calcumaker/calcumaker/firmware/calcumaker-emu/README.md

# calcumaker-emu

The **Calcumaker 16 emulator** — the real calculator on a host terminal.

This is not a look-alike: it hosts the same `calcumaker_core::App` the firmware
runs. Host keys map to the physical **50-key matrix**, presses resolve through
the **f/g shift layers**, and the display is drawn from the **same TM1640
segment bytes** the hardware receives, rendered as LED-style 7-segment art
(Unicode block elements; `--ascii` falls back to plain `_`/`|` for dumb
terminals). If it works here, the only difference on the device is GPIO.

```
┌──────────────────────────────────────────────────────────────────────────────────────────────────┐
│                         ▄▄▄▄        ▄▄▄▄  ▄▄▄▄  ▄▄▄▄  ▄▄▄▄  ▄▄▄▄  ▄▄▄▄  ▄▄▄▄  ▄▄▄▄  ▄▄▄▄  ▄▄▄▄   │
│    █  █▄▄█     █  █▄▄█   ▄▄█     █   ▄▄█  █▄▄   █▄▄    ▄▄█   ▄▄█     █   ▄▄█  █  █  █▄▄█  █▄▄    │
│    █▗    █     █     █  █▄▄▄     █  ▄▄▄█  ▄▄▄█  █▄▄█  █▄▄▄  ▄▄▄█     █  ▄▄▄█  █▄▄█  ▄▄▄█  ▄▄▄█   │
└──────────────────────────────────────────────────────────────────────────────────────────────────┘
 DEC  prec 256  word unbounded
 X: 1.4142135623730950488016887242096980785696718753769480731766797379907324784621
```

The glass **rounds to its 16 digits** like a real HP (`382.1` shows as `382.1`,
never `382.09999…` spilling off the row); the `X:` line underneath is the SHOW
view — the register at full precision.

## Run it

```sh
brew install gmp mpfr    # one-time host deps (apt: libgmp-dev libmpfr-dev)
cargo run                # interactive; ? shows the key map, Ctrl-C quits
```

Keys mirror the device layout (f = gold shift, g = blue shift):

| Host | Calculator |
| --- | --- |
| `0-9` `a-f` `.` | digits (hex digits radix-permitting), decimal point |
| `+ - * /` | arithmetic |
| `Enter` `Bksp` `X` `n` `E` | ENTER, backspace, CLx, CHS, EEX |
| `S C T L Q P I` | sin cos tan ln √x yˣ 1/x |
| `& \| ^ ~ < >` | AND OR XOR NOT SL SR (X by one bit) |
| `H D O B` | HEX DEC OCT BIN |
| `W` `x` `v` | wsize (X bits, 0=∞), swap, roll-down |
| `m` `r` + `0-f` | STO / RCL, then a digit picks the register |
| `F` `G` | f / g shift — `F`,`E` = π; `F`,`I` = prec; `F`,`W` = sign mode (2's/1's/unsgn); `F`,`&`/`\|`/`^` = RL/RR/ASR; `F`,`a-f` = bit set/clr/test, masks, popcount; `G`,`H/D/O/B` = FIX/SCI/ENG/auto |

In word mode the annunciator line shows the sign mode and the **C** (carry) /
**G** (overflow) flags, 16C style.

## Scripted mode (tests, demos, CI)

`--press` feeds a key string and prints the final frame — `;` (or `\n`) is
ENTER:

```sh
cargo run -- --press "2;3+"          # 2 ENTER 3 +      -> 5
cargo run -- --press "2.0Q"          # sqrt(2.0) to 77 digits at prec 256
cargo run -- --press "17Q"           # integer sqrt: 4, C annunciator (inexact)
cargo run -- --press "2;100P"        # exact 2^100 (integers stay integers)
cargo run -- --press "8W;H0f~"       # 8 wsize, hex, NOT 0F -> F0
cargo run -- --press "16W;15nH"      # -15 @16b 2's comp -> FFF1
cargo run -- --press "8W;100;100+"   # wraps to -56, G annunciator
cargo run -- --press "42m3;Xr3"      # STO reg 3, CLx, RCL reg 3 -> 42
cargo run -- --press "4GHFE"         # FIX 4, then pi -> 3.1416
cargo run -- --prec 1024 --press "FE"  # pi at 1024 bits
```

## Relationship to the firmware

`calcumaker-core` owns everything you see here: the keymap + shift layers
(`keys`), entry editing + dispatch (`App`), the engine (`Calc`, GMP + MPFR),
and the 7-seg encoding (`seg7`). The firmware (`../calcumaker-fw`) contributes
only the matrix scan and the TM1640 bus; this crate contributes only the
terminal. One calculator, two I/O bindings.

## License

AGPL-3.0 (see repo root).
