calcumaker/calcumaker/hardware/calcumaker-display/docs/images/display-reference.png

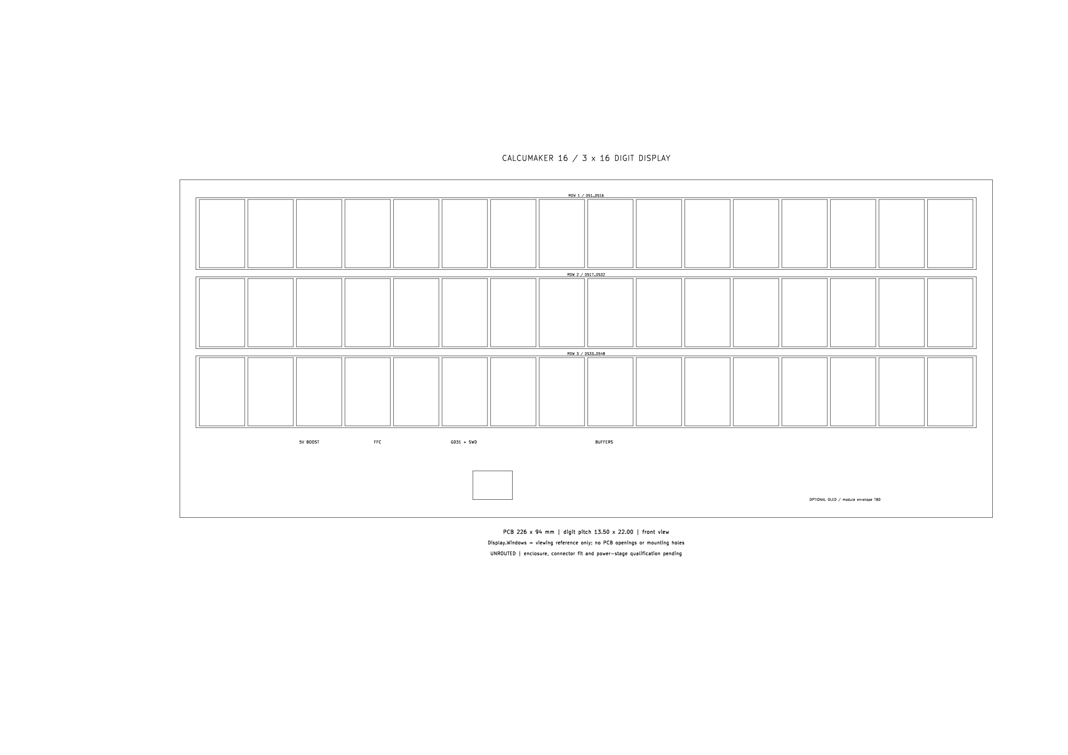
hardware/calcumaker-display/docs/images/display-reference.png
