calcumaker/calcumaker/firmware/calcumaker-matrix-fw/build.rs

//! Put `memory.x` on the linker search path (cortex-m-rt's link.x includes it).
use std::env;
use std::fs::File;
use std::io::Write;
use std::path::PathBuf;

fn main() {
    let out = PathBuf::from(env::var("OUT_DIR").unwrap());
    File::create(out.join("memory.x"))
        .unwrap()
        .write_all(include_bytes!("memory.x"))
        .unwrap();
    println!("cargo:rustc-link-search={}", out.display());
    println!("cargo:rerun-if-changed=memory.x");
    println!("cargo:rerun-if-changed=build.rs");
}
