calcumaker/calcumaker/hardware/scripts/calcumaker-display.schgen.py

#!/usr/bin/env python3
"""Regenerate the Calcumaker 16 **display board** schematic — a KiCad
*multi-channel* design.

    CALCUMAKER_SCHGEN_DRAFT_OK=1 python3 scripts/calcumaker-display.schgen.py
    (or: CALCUMAKER_SCHGEN_DRAFT_OK=1 make gen-calcumaker-display)

The display board is a SEPARATE PCB (split design — it angles up; only the
display serial bus + power cross the interconnect from the MCU board). It holds
the multi-row 7-segment RPN stack (**2-3 rows**; the board is laid out for 3
rows with the top row optionally populated) plus its driver ICs and the
interconnect back to the MCU board.

**Multi-channel structure.** Every row is electrically identical — one TM1640
driving 16 common-cathode digits over the shared 8-segment bus. So the row is
authored ONCE as a reusable, fully-wired child sheet (``display_row.kicad_sch``)
and instantiated **three times** at the root (Row1/Row2/Row3), each annotating
to its own reference designators (U1/DS1-16, U2/DS17-32, U3/DS33-48). This kills
the old redundancy (three hand-copied rows) and the off-page sprawl, and means a
wiring fix in one row propagates to all three.

Digit = **FJ5161AH** (LCSC C8093): a *single-digit* 0.56" common-cathode THT
7-segment (confirmed via LCSC — NOT a 4-digit module; an earlier scaffold
wrongly mapped it to the 4-digit ``CC56-12`` symbol/footprint/3D, which is where
the phantom "clock colon" came from). 16 digits/row => **48 digits** total. The
symbol is authored in ``lib/symbols/calcumaker.kicad_sym`` (standard 5161
pinout); the land is the dimensionally-matched 0.56" single-digit ``LTS6760``.

This is DATA; the engine is scripts/kschgen.py. Verify each lib_id/footprint
exists in your KiCad 10 install before relying on it.
"""
import os, sys
sys.path.insert(0, os.path.dirname(os.path.abspath(__file__)))
import kschgen as K

# --- DRAFT guard -------------------------------------------------------------
if not os.environ.get("CALCUMAKER_SCHGEN_DRAFT_OK"):
    sys.exit(
        "calcumaker-display.schgen.py is a DRAFT (display parts pending final "
        "layout/Isat/pinout verification — see DESIGN.md Display). Set "
        "CALCUMAKER_SCHGEN_DRAFT_OK=1 to generate anyway."
    )

HW = os.path.dirname(os.path.dirname(os.path.abspath(__file__)))   # hardware/
PROJ_DIR = os.path.join(HW, "calcumaker-display")
PROJECT = "calcumaker-display"
PAPER_ROOT = "A3"
PAPER_ROW = "A2"          # a full 16-digit row + its labels wants the bigger sheet

# ---- stable UUIDs. Existing sheets keep their on-disk UUIDs; these constants
#      seed newly scaffolded sheets and keep forced-regeneration diffs readable.
ROOT_UUID = "ca1c0000-0000-4000-8000-0000000d1501"
ROW_FILE  = "ca1c0000-0000-4000-8000-0000000d1510"   # display_row.kicad_sch file id
R1        = "ca1c0000-0000-4000-8000-0000000d1511"   # Row1 sheet symbol
R2        = "ca1c0000-0000-4000-8000-0000000d1512"
R3        = "ca1c0000-0000-4000-8000-0000000d1513"
IC        = "ca1c0000-0000-4000-8000-0000000d1520"   # interconnect sheet + file
AX        = "ca1c0000-0000-4000-8000-0000000d1530"   # aux sheet + file
MCU_SH    = "ca1c0000-0000-4000-8000-0000000d1540"   # module-MCU (STM32G031) sheet + file
PWR_SH    = "ca1c0000-0000-4000-8000-0000000d1550"   # local 5V boost + level shifter sheet + file
ROWS      = [R1, R2, R3]

# ---- symbol libraries -------------------------------------------------------
K.register_stdlib("Connector_Generic", "Conn_01x12", "Conn_01x04")
K.register_lib("calcumaker",
               os.path.join(HW, "lib", "symbols", "calcumaker.kicad_sym"),
               "TM1640", "FJ5161AH")
K.register_stdlib("Device", "R", "C", "L")
K.register_stdlib("MCU_ST_STM32G0", "STM32G031K8Ux")   # module MCU (SPI-slave frame receiver)
K.register_stdlib("Connector", "Conn_ARM_SWD_TagConnect_TC2030-NL")   # G0 SWD (J3)
K.register_stdlib("Converter_DCDC", "TPS61022")        # local VSYS->5V boost (moved off the MCU board)
K.register_stdlib("74xGxx", "74LVC1G125")              # single-gate 3V3->5V shifter (x4: CLK+DIN1/2/3)

# ---- footprint shorthands ---------------------------------------------------
R0402 = "Resistor_SMD:R_0402_1005Metric"
C0402 = "Capacitor_SMD:C_0402_1005Metric"
C0603 = "Capacitor_SMD:C_0603_1608Metric"
L2016 = "Inductor_SMD:L_0805_2012Metric"
G0_FP = "Package_DFN_QFN:UFQFPN-32-1EP_5x5mm_P0.5mm_EP3.5x3.5mm"
SWD_FP = "Connector:Tag-Connect_TC2030-IDC-NL_2x03_P1.27mm_Vertical"
BOOST_FP = "Package_DFN_QFN:Texas_RWU0007A_VQFN-7_2x2mm_P0.5mm"
SOT235 = "Package_TO_SOT_SMD:SOT-23-5"   # single-gate buffer
TM1640_FP = "Package_SO:SOIC-28W_7.5x18.7mm_P1.27mm"   # verify vs TM1640 SOP-28
DIGIT_FP  = "Display_7Segment:7SegmentLED_LTS6760_LTS6780"  # 0.56" single-digit land

# UNIFIED display-module connector pinout (MUST match mcu J3 + the RGB-matrix J1)
UNIFIED_PINS = {1: "VSYS", 2: "VSYS", 3: "GND", 4: "GND", 5: "+3V3",
                6: "SPI_SCLK", 7: "SPI_MOSI", 8: "SPI_CS",
                9: "DISP_IRQ", 10: "DISP_NRST", 11: "DISP_BOOT", 12: "GND"}
RLCSC = {"10k": "C25744", "100k": "C25741", "732k": "", "4.7k": "C25900"}
TITLE = dict(title="Calcumaker 16 — Display", date="2026-07-04", rev="0.2",
             company="calcumaker authors",
             comments=["Programmer's/technical arbitrary-precision RPN calculator",
                       "Display board: multi-channel 7-seg RPN stack + drivers + interconnect (DRAFT)"])

# segment (FJ5161AH pin name) -> TM1640 SEG line. a..g,dp = SEG1..SEG8 (matches
# firmware seg7 bit order: bit0=a .. bit7=dp -> TM1640 SEG1..SEG8).
SEGMAP = {"A": "SEG1", "B": "SEG2", "C": "SEG3", "D": "SEG4",
          "E": "SEG5", "F": "SEG6", "G": "SEG7", "DP": "SEG8"}

G = 2.54          # 100-mil grid; placements MUST snap to it so pin endpoints,
                  # stubs and labels stay on the 50-mil ERC grid.


def g(n):
    return n * G


def _C(value, fp):
    return dict(lib_id="Device:C", value=value, fp=fp,
                lcsc={"10uF": "C15850", "100nF": "C1525"}.get(value, ""))


# ---- helpers for the placed-not-wired module sheets (MCU + local 5V power) ---
CLCSC = {"100nF": "C1525", "4.7uF": "C23630", "10uF": "C15850", "22uF": "C45783"}


def R(ref, val):
    return dict(ref=ref, lib_id="Device:R", value=val, fp=R0402, lcsc=RLCSC.get(val, ""))


def C(ref, val, fp=C0402):
    return dict(ref=ref, lib_id="Device:C", value=val, fp=fp, lcsc=CLCSC.get(val, ""))


def place1(path, specs, x0=g(8), y0=g(14), dx=g(16), dy=g(14), per=6):
    comps = []
    for idx, sp in enumerate(specs):
        ref = sp["ref"]
        c = {k: v for k, v in sp.items() if k != "ref"}
        c["x"] = x0 + (idx % per) * dx
        c["y"] = y0 + (idx // per) * dy
        comps.append((c, [(path, ref)]))
    return comps


# ============================ reusable ROW sheet =============================
# One TM1640 + 16 single-digit FJ5161AH, fully wired. Instantiated x3 at root.
def build_row():
    comps = []      # (comp_dict, [(path, ref), ...])
    wiring = ""

    def paths_refs(fn):
        return [(f"/{ROOT_UUID}/{ROWS[i]}", fn(i)) for i in range(3)]

    # --- driver -------------------------------------------------------------
    U = dict(lib_id="calcumaker:TM1640", value="TM1640", fp=TM1640_FP,
             lcsc="C5337152", mpn="TM1640", mfr="TitanMicro", x=g(25), y=g(60))
    comps.append((U, paths_refs(lambda i: f"U{i+1}")))
    for n in range(1, 9):
        wiring += K.net_pin(U, f"SEG{n}", f"SEG{n}")                  # left bus
    for n in range(1, 17):
        wiring += K.net_pin(U, f"GRID{n}", f"GRID{n}")               # right, per digit
    wiring += K.net_pin(U, "VDD", "+5V", kind="glabel")
    wiring += K.net_pin(U, "VSS", "GND", kind="glabel")
    wiring += K.net_pin(U, "SCLK", "DISP_CLK", kind="glabel")         # shared clock
    wiring += K.net_pin(U, "DIN", "DIN", kind="hlabel", shape="input")  # per-row -> sheet pin

    # --- 16 digits (8 across x 2 down) --------------------------------------
    for k in range(1, 17):
        col, row = (k - 1) % 8, (k - 1) // 8
        dg = dict(lib_id="calcumaker:FJ5161AH", value="FJ5161AH", fp=DIGIT_FP,
                  lcsc="C8093", mpn="FJ5161AH", mfr="Shenzhen Zhihao",
                  x=g(52 + col * 22), y=g(36 + row * 35))
        comps.append((dg, paths_refs(lambda i, kk=k: f"DS{kk + 16 * i}")))
        for seg, net in SEGMAP.items():
            wiring += K.net_pin(dg, seg, net)          # segments -> shared SEG bus
        wiring += K.net_pin(dg, 3, f"GRID{k}")         # both commons -> this digit's grid
        wiring += K.net_pin(dg, 8, f"GRID{k}")

    # --- decoupling + bulk per row ------------------------------------------
    cdec = dict(_C("100nF", C0402), x=g(16), y=g(78))    # below the driver, clear of its labels
    comps.append((cdec, paths_refs(lambda i: f"C{i+1}")))          # C1/C2/C3
    wiring += K.net_pin(cdec, 1, "+5V", kind="glabel")
    wiring += K.net_pin(cdec, 2, "GND", kind="glabel")
    cbulk = dict(_C("10uF", C0603), x=g(26), y=g(78))
    comps.append((cbulk, paths_refs(lambda i: f"C{i+4}")))         # C4/C5/C6
    wiring += K.net_pin(cbulk, 1, "+5V", kind="glabel")
    wiring += K.net_pin(cbulk, 2, "GND", kind="glabel")

    note = (20.0, 240.0, K.note_block(
        "REUSABLE ROW  (multi-channel: instantiated x3 as Row1/Row2/Row3)",
        "  Row1 -> U1 / DS1-16     Row2 -> U2 / DS17-32     Row3 -> U3 / DS33-48",
        "",
        "One TM1640 (C5337152) drives 16x FJ5161AH single-digit 0.56\" common-",
        "cathode (C8093, THROUGH-HOLE):",
        "  SEG1..8 (a..g,dp)  -  shared 8-line bus to all 16 digits' segments",
        "  GRID1..16          -  one per digit  (GRID k -> digit k cathode)",
        "  VDD  -> +5V              VSS  -> GND",
        "  SCLK -> DISP_CLK (global net, shared by all 3 rows)",
        "  DIN  -> hierarchical pin (Row1<-DIN1, Row2<-DIN2, Row3<-DIN3 @ root)",
        "",
        "Runs at +5V (VDD + LED) from the MCU-board EN-gated 5V boost.",
        "Digit->GRID is 1:1 sequential; firmware seg7/App is the source of truth.",
        "*** THT digits (no SMD multi-digit 7-seg on LCSC). ***",
        "Verify FJ5161AH pad map vs the LTS6760 0.56\" land before fab."))
    return dict(uuid=ROW_FILE, file="display_row.kicad_sch", page="2",
                title="Reusable 7-seg row (1x TM1640 + 16 digits)",
                comps=comps, wiring=wiring, notes=[note], _dir=PROJ_DIR)


# ============================ interconnect sheet ============================
def build_interconnect():
    path = f"/{ROOT_UUID}/{IC}"
    # 0.5mm 12P FFC to the MCU board — the UNIFIED display-module connector
    # (same part + pinout as the RGB-matrix board's J1 and mcu J3, so the two
    # display modules are INTERCHANGEABLE). Now a technology-agnostic SPI bus:
    # power + SPI "display intent" + reset/boot. The module MCU (STM32G031) is
    # the SPI slave; it renders locally to the 3 TM1640s. 5V + level-shifting are
    # generated LOCALLY (DispPower sheet), so +5V no longer crosses the FFC.
    # CABLE = GCT FFC05-TIN 05-12-A-<len>-A-4-06-4-T (DigiKey non-BOM; len TBD).
    J1 = dict(lib_id="Connector_Generic:Conn_01x12", value="TO MCU (unified SPI FFC)",
              fp="Connector_FFC-FPC:Hirose_FH12-12S-0.5SH_1x12-1MP_P0.50mm_Horizontal",
              lcsc="C262661", mpn="AFC01-S12FCA-00", mfr="JUSHUO", x=g(28), y=g(28))
    wiring = ""
    for pin, net in UNIFIED_PINS.items():
        wiring += K.net_pin(J1, pin, net, kind="glabel")
    C7 = dict(_C("10uF", C0603), x=g(48), y=g(28))
    wiring += K.net_pin(C7, 1, "VSYS", kind="glabel")     # bulk on the incoming VSYS
    wiring += K.net_pin(C7, 2, "GND", kind="glabel")
    comps = [(J1, [(path, "J1")]), (C7, [(path, "C7")])]
    note = (20.0, 120.0, K.note_block(
        "UNIFIED DISPLAY-MODULE CONNECTOR  -  J1  AFC01-S12FCA-00  (LCSC C262661)",
        "0.5mm 12-pos FFC to the MCU board. SAME connector + pinout as the RGB-",
        "matrix board's J1 and mcu J3 -> the display modules are INTERCHANGEABLE.",
        "",
        K.pin_table([(1, "VSYS"), (2, "VSYS"), (3, "GND"), (4, "GND"), (5, "+3V3"),
                     (6, "SPI_SCLK"), (7, "SPI_MOSI"), (8, "SPI_CS"), (9, "DISP_IRQ"),
                     (10, "DISP_NRST (G0 NRST)"), (11, "DISP_BOOT (G0 BOOT0)"),
                     (12, "GND")]),
        "",
        "VSYS -> the local 5V boost (DispPower); +3V3 -> the module G0. SPI = the",
        "main MCU writes display intent; the G0 renders to the 3 TM1640s. No I2C /",
        "no CLK/DIN on the FFC anymore (all local). DISP_IRQ = module ready.",
        "CABLE (non-BOM): GCT FFC05-TIN 05-12-A-<len>-A-4-06-4-T (DigiKey; len TBD)."))
    return dict(uuid=IC, file="interconnect.kicad_sch", page="6",
                title="MCU board interconnect (0.5mm FFC)", comps=comps,
                wiring=wiring, notes=[note], _dir=PROJ_DIR)


# ====================== aux display sheet (DNP-optional) ====================
def build_aux():
    path = f"/{ROOT_UUID}/{AX}"
    J2 = dict(lib_id="Connector_Generic:Conn_01x04", value="OLED 128x32 (DNP)",
              fp="Connector_PinHeader_2.54mm:PinHeader_1x04_P2.54mm_Vertical",
              lcsc="C2691448", mpn="PZ254V-11-04P", mfr="XKB", dnp=True,
              x=g(28), y=g(28))
    j2nets = {1: "+3V3", 2: "GND", 3: "SCL", 4: "SDA"}
    wiring = ""
    for pin, net in j2nets.items():
        wiring += K.net_pin(J2, pin, net, kind="glabel")
    note = (20.0, 110.0, K.note_block(
        "AUX OLED  -  J2   (OPTIONAL, DNP by default)",
        "Receives a 0.91\" SSD1306 128x32 I2C module (sourced separately,",
        "hand-placed with the THT digits).  I2C at 3V3 straight from the MCU",
        "(pull-ups on the MCU board, DNP alongside).",
        "",
        K.pin_table([(1, "VCC <- +3V3"), (2, "GND"), (3, "SCL"), (4, "SDA")], cols=1),
        "",
        "Shows full error text / SETUP / STATUS; the 7-seg glass stays primary."))
    return dict(uuid=AX, file="aux-display.kicad_sch", page="7",
                title="Aux OLED 128x32 (SSD1306 I2C) — DNP-optional",
                comps=[(J2, [(path, "J2")])], wiring=wiring, notes=[note],
                _dir=PROJ_DIR)


# ================= module MCU sheet (STM32G031, SPI-slave) ===================
def build_disp_mcu():
    path = f"/{ROOT_UUID}/{MCU_SH}"
    comps, w = [], ""

    def one(c, ref):
        comps.append((c, [(path, ref)]))
        return c

    # STM32G031K8Ux (33 pins; symbol extends STM32G031K_4-6-8_Ux). Wire by number.
    U4 = one(dict(lib_id="MCU_ST_STM32G0:STM32G031K8Ux", value="STM32G031K8U6",
                  fp=G0_FP, lcsc="C432207", mpn="STM32G031K8U6",
                  mfr="STMicroelectronics", x=g(40), y=g(44)), "U4")
    w += K.net_pin(U4, 4, "+3V3", kind="glabel")          # VDD
    w += K.net_pin(U4, 5, "GND", kind="glabel")           # VSS
    w += K.net_pin(U4, 33, "GND", kind="glabel")          # VSS/EP
    w += K.net_pin(U4, 6, "DISP_NRST", kind="glabel")     # PF2/NRST
    w += K.net_pin(U4, 7, "DISP_IRQ", kind="glabel")      # PA0 -> IRQ out
    w += K.net_pin(U4, 11, "SPI_CS", kind="glabel")       # PA4  SPI1 NSS
    w += K.net_pin(U4, 12, "SPI_SCLK", kind="glabel")     # PA5  SPI1 SCK
    w += K.net_pin(U4, 14, "SPI_MOSI", kind="glabel")     # PA7  SPI1 MOSI
    w += K.net_pin(U4, 24, "SWDIO", kind="label")         # PA13
    w += K.net_pin(U4, 25, "SWCLK", kind="label")         # PA14
    w += K.net_pin(U4, 15, "CLK_3V3", kind="glabel")      # PB0 -> shifter -> DISP_CLK
    w += K.net_pin(U4, 16, "DIN1_3V3", kind="glabel")     # PB1 -> DIN1
    w += K.net_pin(U4, 17, "DIN2_3V3", kind="glabel")     # PB2 -> DIN2
    w += K.net_pin(U4, 27, "DIN3_3V3", kind="glabel")     # PB3 -> DIN3
    w += K.net_pin(U4, 30, "OLED_SCL", kind="glabel")     # PB6 I2C1 SCL
    w += K.net_pin(U4, 31, "OLED_SDA", kind="glabel")     # PB7 I2C1 SDA

    # decoupling + reset
    for i, (ref, val, fp) in enumerate([("C8", "100nF", C0402), ("C9", "100nF", C0402),
                                        ("C10", "100nF", C0402), ("C11", "4.7uF", C0603)]):
        c = one(dict(C(ref, val, fp), x=g(8 + i * 5), y=g(66)), ref)
        w += K.net_pin(c, 1, "+3V3", kind="glabel")
        w += K.net_pin(c, 2, "GND", kind="glabel")
    C12 = one(dict(C("C12", "100nF"), x=g(30), y=g(66)), "C12")       # NRST cap
    w += K.net_pin(C12, 1, "DISP_NRST", kind="glabel")
    w += K.net_pin(C12, 2, "GND", kind="glabel")
    R1 = one(dict(R("R1", "10k"), x=g(36), y=g(66)), "R1")            # BOOT0/DISP_BOOT pulldown
    w += K.net_pin(R1, 1, "DISP_BOOT", kind="glabel")
    w += K.net_pin(R1, 2, "GND", kind="glabel")

    # SWD Tag-Connect
    J3 = one(dict(lib_id="Connector:Conn_ARM_SWD_TagConnect_TC2030-NL",
                  value="SWD TC2030-NL", fp=SWD_FP, x=g(60), y=g(44)), "J3")
    w += K.net_pin(J3, 1, "+3V3", kind="glabel")
    w += K.net_pin(J3, 2, "SWDIO", kind="label")
    w += K.net_pin(J3, 3, "DISP_NRST", kind="glabel")
    w += K.net_pin(J3, 4, "SWCLK", kind="label")
    w += K.net_pin(J3, 5, "GND", kind="glabel")

    note = (15, 84, K.note_block(
        "MODULE MCU (WIRED)  -  U4 STM32G031K8U6 (C432207, UFQFPN-32)",
        "SPI-slave frame receiver -> renders 'display intent' to the 3 TM1640s.",
        "POWER  VDD(4)->+3V3 (C8/C9 100nF + C11 4.7uF); VSS(5,33)->GND.",
        "RESET  NRST=PF2(6)->DISP_NRST + C12 100nF.  BOOT0: R1 10k on DISP_BOOT;",
        "       route to the G031 BOOT0/option-byte at layout (UART-boot entry).",
        "LINK   SPI1 PA5/PA7/PA4 <- SPI_SCLK/MOSI/CS;  PA0 -> DISP_IRQ.",
        "DRIVE  PB0-3 -> CLK_3V3 + DIN1/2/3_3V3 (3V3) -> DispPower shifters -> 5V",
        "       to the TM1640s (Row1-3). CLOCK internal HSI.",
        "OLED   PB6/PB7 = I2C1 SCL/SDA -> AuxDisplay J2.  PROG  J3 SWD Tag-Connect."))
    return dict(uuid=MCU_SH, file="disp_mcu.kicad_sch", page="8",
                title="Module MCU (STM32G031K8U6, SPI-slave) — wired",
                comps=comps, wiring=w, notes=[note], _dir=PROJ_DIR)


# ============ local 5V boost + level shifter sheet (VSYS->5V) ================
def build_disp_power():
    path = f"/{ROOT_UUID}/{PWR_SH}"
    comps, w = [], ""

    def one(c, ref):
        comps.append((c, [(path, ref)]))
        return c

    # VSYS -> +5V boost (TPS61022, adjustable)
    U5 = one(dict(lib_id="Converter_DCDC:TPS61022", value="TPS61022RWUR", fp=BOOST_FP,
                  lcsc="C915088", mpn="TPS61022RWUR", mfr="Texas Instruments",
                  x=g(30), y=g(44)), "U5")
    w += K.net_pin(U5, 7, "VSYS", kind="glabel")          # VIN
    w += K.net_pin(U5, 2, "SW", kind="label")             # SW node (to L1)
    w += K.net_pin(U5, 3, "+5V", kind="glabel")           # VOUT
    w += K.net_pin(U5, 4, "FB", kind="label")             # feedback
    w += K.net_pin(U5, 5, "VSYS", kind="glabel")          # EN -> always on (gate off = a GPIO later)
    w += K.net_pin(U5, 6, "GND", kind="glabel")           # MODE -> GND (forced PWM)
    w += K.net_pin(U5, 1, "GND", kind="glabel")           # GND
    L1 = one(dict(lib_id="Device:L", value="1uH", fp=L2016, lcsc="C5832342",
                  mpn="FTC201610S1R0MBCA", mfr="Sunlord", x=g(18), y=g(40)), "L1")
    w += K.net_pin(L1, 1, "VSYS", kind="glabel")
    w += K.net_pin(L1, 2, "SW", kind="label")
    C13 = one(dict(C("C13", "10uF", C0603), x=g(10), y=g(50)), "C13")   # Cin
    w += K.net_pin(C13, 1, "VSYS", kind="glabel")
    w += K.net_pin(C13, 2, "GND", kind="glabel")
    for i, ref in enumerate(("C14", "C15")):                            # Cout 2x22uF
        c = one(dict(C(ref, "22uF", C0603), x=g(46 + i * 5), y=g(50)), ref)
        w += K.net_pin(c, 1, "+5V", kind="glabel")
        w += K.net_pin(c, 2, "GND", kind="glabel")
    R2 = one(dict(R("R2", "732k"), x=g(44), y=g(38)), "R2")             # FB divider hi
    w += K.net_pin(R2, 1, "+5V", kind="glabel")
    w += K.net_pin(R2, 2, "FB", kind="label")
    R3 = one(dict(R("R3", "100k"), x=g(44), y=g(58)), "R3")             # FB divider lo
    w += K.net_pin(R3, 1, "FB", kind="label")
    w += K.net_pin(R3, 2, "GND", kind="glabel")

    # 4x single-gate HCT shifter: A <- x_3V3 (G031), Y -> x (5V to the TM1640s).
    # HCT (VIH=2V @5V) accepts 3V3 cleanly. VCC=+5V, /OE=GND.
    for i, (a, y) in enumerate([("CLK_3V3", "DISP_CLK"), ("DIN1_3V3", "DIN1"),
                                ("DIN2_3V3", "DIN2"), ("DIN3_3V3", "DIN3")]):
        U = one(dict(lib_id="74xGxx:74LVC1G125", value="74HCT1G125", fp=SOT235,
                     lcsc="C547448", mpn="74HCT1G125GW", mfr="Nexperia",
                     x=g(8 + i * 15), y=g(70)), f"U{6 + i}")
        w += K.net_pin(U, 5, "+5V", kind="glabel")         # VCC
        w += K.net_pin(U, 3, "GND", kind="glabel")         # GND
        w += K.net_pin(U, 1, "GND", kind="glabel")         # /OE low = enabled
        w += K.net_pin(U, 2, a, kind="glabel")             # A  <- G031 (3V3)
        w += K.net_pin(U, 4, y, kind="glabel")             # Y  -> TM1640s (5V)
        cc = one(dict(C(f"C{16 + i}", "100nF"), x=g(8 + i * 15), y=g(80)), f"C{16 + i}")
        w += K.net_pin(cc, 1, "+5V", kind="glabel")
        w += K.net_pin(cc, 2, "GND", kind="glabel")

    note = (15, 90, K.note_block(
        "LOCAL 5V RAIL + LEVEL SHIFT (WIRED)  -  moved off the MCU board.",
        "5V BOOST  U5 TPS61022 (C915088): VIN<-VSYS, L1 1uH (VSYS->SW), Cin C13",
        "  10uF, Cout C14/C15 2x22uF; FB R2 732k / R3 100k -> +5V (Vref 0.6V).",
        "  EN->VSYS (always on; tie to a G031 GPIO to gate off in deep sleep).",
        "SHIFT  U6-U9 74HCT1G125 @ +5V (VIH=2V accepts 3V3): A <- G031 CLK/DIN1/2/3",
        "  (3V3), Y -> DISP_CLK + DIN1/2/3 (5V) to the TM1640s. /OE=GND; C16-19",
        "  decouple. *** VERIFY the 74HCT1G125GW package (SOT-353 vs the SOT-23-5",
        "  land) at layout, or pick the SOT-23-5-packaged HCT1G125. ***"))
    return dict(uuid=PWR_SH, file="disp_power.kicad_sch", page="9",
                title="Local 5V boost (TPS61022) + 4x 74HCT1G125 level shifter — wired",
                comps=comps, wiring=w, notes=[note], _dir=PROJ_DIR)


# ============================ root sheet ====================================
def build_root_strings():
    # 3 reused row instances + interconnect + aux, with per-row DIN routed to
    # DIN1/2/3 global labels.
    sym = ""
    wiring = ""
    for i, (uuid, name) in enumerate([(R1, "Row1"), (R2, "Row2"), (R3, "Row3")]):
        x, y = g(28), g(12 + i * 12)
        w, h = g(24), g(8)
        py = y + g(4)
        sym += K.w_sheet(name, "display_row.kicad_sch", uuid, x, y, w, h,
                         pins=[("DIN", "input", x, py, 180)])
        wiring += K.w_wire(x, py, x - g(3), py)
        wiring += K.w_glabel(f"DIN{i+1}", x - g(3), py, 180, shape="output")
    sym += K.w_sheet("Interconnect", "interconnect.kicad_sch", IC,
                     g(64), g(12), g(20), g(8), pins=[])
    sym += K.w_sheet("AuxDisplay", "aux-display.kicad_sch", AX,
                     g(64), g(24), g(20), g(8), pins=[])
    sym += K.w_sheet("DispMCU", "disp_mcu.kicad_sch", MCU_SH,
                     g(64), g(36), g(20), g(8), pins=[])
    sym += K.w_sheet("DispPower", "disp_power.kicad_sch", PWR_SH,
                     g(64), g(48), g(20), g(8), pins=[])
    wiring += K.text_note(
        "Calcumaker 16 — Display (MULTI-CHANNEL). Row1/2/3 are three instances "
        "of ONE reusable sheet (display_row.kicad_sch). Shared bus is carried on "
        "global nets +5V / GND / DISP_CLK; each row's serial data DIN is a "
        "hierarchical pin fed by DIN1/DIN2/DIN3 from the interconnect. Top row "
        "(Row3 / U3 / DS33-48) is optional -> 2- or 3-row build.", 20.0, 105.0)
    pro_sheets = [[R1, "Row1"], [R2, "Row2"], [R3, "Row3"],
                  [IC, "Interconnect"], [AX, "AuxDisplay"],
                  [MCU_SH, "DispMCU"], [PWR_SH, "DispPower"]]
    return sym, wiring, pro_sheets


# ============================ generate ======================================
row = build_row()
interconnect = build_interconnect()
aux = build_aux()

print("child sheets:")
K.write_wired_child(row, PROJECT, ROOT_UUID, TITLE, PAPER_ROW)
K.write_wired_child(interconnect, PROJECT, ROOT_UUID, TITLE, PAPER_ROOT)
K.write_wired_child(aux, PROJECT, ROOT_UUID, TITLE, PAPER_ROOT)
K.write_wired_child(build_disp_mcu(), PROJECT, ROOT_UUID, TITLE, PAPER_ROOT)
K.write_wired_child(build_disp_power(), PROJECT, ROOT_UUID, TITLE, PAPER_ROOT)

sym, wiring, pro_sheets = build_root_strings()
K.write_root(PROJECT, PROJ_DIR, ROOT_UUID, TITLE, sym, wiring, pro_sheets,
             paper=PAPER_ROOT)

# remove the now-obsolete flat display.kicad_sch (replaced by display_row.kicad_sch)
_old = os.path.join(PROJ_DIR, "display.kicad_sch")
if os.path.exists(_old) and os.environ.get("KSCHGEN_FORCE") == "1":
    os.remove(_old)
    print("removed obsolete display.kicad_sch (replaced by display_row.kicad_sch)")
elif os.path.exists(_old):
    print("kept obsolete display.kicad_sch (set KSCHGEN_FORCE=1 to remove)")
